c-mauderer/Master-Clock/Measurements/current_estimate_100uF.csv

Device OWON HDS2102S found at port 3:4
2024-01-21 08:49:11.843626 | 000.20 mA
2024-01-21 08:49:12.261659 | 000.21 mA
2024-01-21 08:49:12.679595 | 000.21 mA
2024-01-21 08:49:13.097644 | 000.22 mA
2024-01-21 08:49:13.514580 | 000.22 mA
2024-01-21 08:49:13.933602 | 000.21 mA
2024-01-21 08:49:14.351605 | 000.21 mA
2024-01-21 08:49:14.769608 | 000.21 mA
2024-01-21 08:49:15.187604 | 000.20 mA
2024-01-21 08:49:15.605582 | 000.21 mA
2024-01-21 08:49:16.023560 | 000.21 mA
2024-01-21 08:49:16.440503 | 000.21 mA
2024-01-21 08:49:16.858577 | 000.22 mA
2024-01-21 08:49:17.276501 | 000.21 mA
2024-01-21 08:49:17.694500 | 000.21 mA
2024-01-21 08:49:18.112520 | 000.21 mA
2024-01-21 08:49:18.529483 | 000.21 mA
2024-01-21 08:49:18.948520 | 000.21 mA
2024-01-21 08:49:19.366466 | 000.21 mA
2024-01-21 08:49:19.784502 | 000.21 mA
2024-01-21 08:49:20.201432 | 000.21 mA
2024-01-21 08:49:20.619424 | 000.21 mA
2024-01-21 08:49:21.038420 | 000.21 mA
2024-01-21 08:49:21.456410 | 000.21 mA
2024-01-21 08:49:21.874421 | 000.21 mA
2024-01-21 08:49:22.292423 | 000.21 mA
2024-01-21 08:49:22.710408 | 000.21 mA
2024-01-21 08:49:23.128407 | 000.21 mA
2024-01-21 08:49:23.546412 | 000.21 mA
2024-01-21 08:49:23.964398 | 000.21 mA
2024-01-21 08:49:24.381385 | 000.22 mA
2024-01-21 08:49:24.798366 | 000.22 mA
2024-01-21 08:49:25.216343 | 000.22 mA
2024-01-21 08:49:25.634364 | 000.22 mA
2024-01-21 08:49:26.051325 | 000.22 mA
2024-01-21 08:49:26.469313 | 000.22 mA
2024-01-21 08:49:26.888310 | 000.21 mA
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
2024-01-21 09:10:32.809375 | 000.14 mA
2024-01-21 09:10:33.227397 | 000.14 mA
2024-01-21 09:10:33.645353 | 000.14 mA
2024-01-21 09:10:34.063371 | 000.14 mA
2024-01-21 09:10:34.481383 | 000.14 mA
2024-01-21 09:10:34.899312 | 000.14 mA
2024-01-21 09:10:35.317302 | 000.14 mA
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
