c-mauderer/Master-Clock/Measurements/current_final_10V.csv

Mode | Time(s) | Value
DCI | 0.0043460000 | 1.015082E-04
DCI | 0.0264199991 | 1.022343E-04
DCI | 0.0403130017 | 9.600027E-05
DCI | 0.0537340008 | 9.128778E-05
DCI | 0.0705669969 | 9.811835E-05
DCI | 0.0875149965 | 1.011891E-04
DCI | 0.1013320014 | 1.016654E-04
DCI | 0.1148680001 | 9.636562E-05
DCI | 0.1285540015 | 9.746628E-05
DCI | 0.1418350041 | 9.986646E-05
DCI | 0.1586000025 | 9.524184E-05
DCI | 0.1722420007 | 9.253181E-05
DCI | 0.1890670061 | 9.690670E-05
DCI | 0.2029470056 | 1.001532E-04
DCI | 0.2164340019 | 9.421517E-05
DCI | 0.2332800031 | 9.339661E-05
DCI | 0.2472680062 | 9.778538E-05
DCI | 0.2607350051 | 9.989883E-05
DCI | 0.2773639858 | 9.640262E-05
DCI | 0.2911269963 | 9.275379E-05
DCI | 0.3046770096 | 1.017394E-04
DCI | 0.3213509917 | 1.007128E-04
DCI | 0.3356040120 | 9.426604E-05
DCI | 0.3490389884 | 9.874268E-05
DCI | 0.3654910028 | 1.013787E-04
DCI | 0.3795289993 | 9.483949E-05
DCI | 0.3932430148 | 9.494586E-05
DCI | 0.4101929963 | 9.321163E-05
DCI | 0.4240120053 | 1.019614E-04
DCI | 0.4376859963 | 9.776226E-05
DCI | 0.4541350007 | 9.318850E-05
DCI | 0.4680350125 | 9.960748E-05
DCI | 0.4820350111 | 9.767901E-05
DCI | 0.4990069866 | 9.712868E-05
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
