c-mauderer/Master-Clock/Measurements/current_final_3V.csv

Mode | Time(s) | Value
DCI | 0.0054250001 | 3.465068E-04
DCI | 0.0298410002 | 3.501927E-04
DCI | 0.0446350016 | 3.459288E-04
DCI | 0.0591930002 | 3.392138E-04
DCI | 0.0738409981 | 3.498967E-04
DCI | 0.0917920023 | 3.501418E-04
DCI | 0.1066310033 | 3.436812E-04
DCI | 0.1251060069 | 3.452582E-04
DCI | 0.1400399953 | 3.390658E-04
DCI | 0.1544400007 | 3.434315E-04
DCI | 0.1688449979 | 3.509974E-04
DCI | 0.1874009967 | 3.462664E-04
DCI | 0.2021870017 | 3.436812E-04
DCI | 0.2203149945 | 3.416695E-04
DCI | 0.2354809940 | 3.438199E-04
DCI | 0.2499119937 | 3.487498E-04
DCI | 0.2680949867 | 3.475335E-04
DCI | 0.2832210064 | 3.405735E-04
DCI | 0.2977829874 | 3.419285E-04
DCI | 0.3159480095 | 3.437876E-04
DCI | 0.3310259879 | 3.506968E-04
DCI | 0.3492319882 | 3.492724E-04
DCI | 0.3639410138 | 3.445183E-04
DCI | 0.3788839877 | 3.395422E-04
DCI | 0.3932139874 | 3.514598E-04
DCI | 0.4112290144 | 3.513072E-04
DCI | 0.4265179932 | 3.529582E-04
DCI | 0.4449830055 | 3.424326E-04
DCI | 0.4595699906 | 3.391167E-04
DCI | 0.4742369950 | 3.456328E-04
DCI | 0.4886209965 | 3.502759E-04
DCI | 0.5066930056 | 3.510621E-04
DCI | 0.5290750265 | 3.477462E-04
DCI | 0.5437849760 | 3.403746E-04
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
