c-mauderer/Master-Clock/Hardware/Simulation_OPV_only/Simulation_OPV_only.asc

B1: bv; V={idt(V(in)*-I(R2))/3600}
C3: cap; 10µ; V=50 Irms=0 Rser=0.0051 Lser=500p mfg="Würth Elektronik" pn="885012210031 WCAP-CSGP 1812" type="X7R"
C4: cap; 1000µ
L2: ind; 0.1
R1: res; 1k
R2: res; 10
R3: res; 1k
R5: res; 2k
U1: LT1178
V1: voltage; 24
V2: voltage; PULSE(0 3 0 1u 1u 60s 120s)
V3: voltage; 1
Named nets: 0, reg, uhr, switch, opout, Energie, in
.tran 0 3600s 0 10m
Voltage equals Energy in Wh
Candidates for OPV:
LT1178
OP193
