c-mauderer/Master-Clock/Hardware/Simulation_DCDC+OPV/Entwurf.asc

C1: cap; 4.7µ; V=100 Irms=0 Rser=0.0043 Lser=1.3n mfg="Würth Elektronik" pn="885012214003 WCAP-CSGP 2220" type="X7R"
C2: cap; 1µ; V=16 Irms=0 Rser=0.0237 Lser=872p mfg="Würth Elektronik" pn="885382207001 WCAP-CSST 0805" type="X7R"
C3: cap; 10µ; V=50 Irms=0 Rser=0.0051 Lser=500p mfg="Würth Elektronik" pn="885012210031 WCAP-CSGP 1812" type="X7R"
C4: cap; 100µ
D1: schottky; PMEG6010AED
L1: ind; 1000n; Ipk=1.8 Rser=0.064 Rpar=4276.7 Cpar=424f mfg="Würth Elektronik" pn="744045001 WE-LQ 1812"
L2: ind; 0.1
R2: res; 1
R3: res; 1000k
R4: res; 71k
R5: res; 2k
U1: LT8330
U2: OP292
V1: voltage; 4.5
V2: voltage; PULSE(0 3 0 1u 1u 100m 200m)
V3: voltage; 1
Named nets: 0, reg, in, uhr, switch, opout
.tran 1s
.options abstol=1e-3 reltol=0.02
.ic V(out)=18 V(in)=4.5
