c-mauderer/Master-Clock/Hardware/Simulation_DCDC/DCDC.asc

B1: bv; V={idt(V(src)*-I(R2))/3600}
C1: cap; 4.7µ; V=100 Irms=0 Rser=0.0043 Lser=1.3n mfg="Würth Elektronik" pn="885012214003 WCAP-CSGP 2220" type="X7R"
C2: cap; 1µ; V=16 Irms=0 Rser=0.0237 Lser=872p mfg="Würth Elektronik" pn="885382207001 WCAP-CSST 0805" type="X7R"
C3: cap; 10µ; V=50 Irms=0 Rser=0.0051 Lser=500p mfg="Würth Elektronik" pn="885012210031 WCAP-CSGP 1812" type="X7R"
D1: schottky; PMEG6010AED
L1: ind; 1000n; Ipk=1.8 Rser=0.064 Rpar=4276.7 Cpar=424f mfg="Würth Elektronik" pn="744045001 WE-LQ 1812"
R2: res; 1
R3: res; 1000k
R4: res; 71k
U1: LT8330
V1: voltage; 4.5
Named nets: 0, reg, in, Energie_Wh, src
.tran 1s
.options abstol=1e-6 reltol=0.003
.ic V(out)=22 V(in)=4.5
